Pealie/Thin-Pod-Gateway-rev-0.1/docs/observability/Thin-Pod_Memfault_nRFCloud_PR_Notes.md

# Pull Request Notes: Memfault / nRF Cloud Observability Evaluation

## PR title

Add Memfault nRF Cloud observability evaluation

## PR base and compare branches

```text
base:    gateway-rev0.1-completion-checklist
compare: memfault-nrfcloud-evaluation
```

## PR description

Adds a bounded evaluation of Memfault / nRF Cloud as an optional observability and OTA layer for the Thin-Pod Gateway / Nordic / Zephyr path.

The document positions Memfault / nRF Cloud as suitable for firmware health, reboot diagnostics, crash capture, update history and fleet-level operational metrics, while explicitly keeping the project’s open telemetry, DSP feature extraction, vibration logging and predictive-maintenance analysis pipeline independent.

## Added

- `docs/observability/Thin-Pod_Memfault_nRFCloud_Evaluation.md`

## Scope

This is a documentation-only change.

No firmware, hardware, schematic, PCB, Gateway interface, UWB transport or telemetry-schema changes are introduced by this PR.

## Notes

Memfault / nRF Cloud is treated as optional and non-core.

The open reproducibility path remains:

- local logging;
- Gateway telemetry;
- DSP feature records;
- vibration-analysis outputs;
- repository-held validation evidence;
- CSV / JSON export where appropriate.

The document makes clear that Memfault / nRF Cloud should be used to observe device and firmware health, not to define the core predictive-maintenance data path.

## Recommended conclusion

Memfault / nRF Cloud is suitable as an optional Nordic / Zephyr observability and OTA layer for Thin-Pod nodes and Gateway-side Nordic modules. It should be used for firmware health, reboot diagnostics, crash capture, update history and fleet-level operational metrics. It should not replace the project’s open telemetry, DSP feature extraction, vibration-data logging or predictive-maintenance analysis pipeline.

## Suggested review checklist

- [ ] The document is correctly located under `docs/observability/`.
- [ ] The integration is clearly described as optional.
- [ ] The core Thin-Pod telemetry and DSP path remains open and independent.
- [ ] No credentials, API keys, cloud project IDs or private Memfault / nRF Cloud values are included.
- [ ] The document does not imply that Memfault / nRF Cloud is required for OSHWA reproducibility.
- [ ] The branch contains only the intended documentation file.

## Suggested merge action

If the PR diff shows only:

```text
A       docs/observability/Thin-Pod_Memfault_nRFCloud_Evaluation.md
```

then the PR is clean and suitable to merge into:

```text
gateway-rev0.1-completion-checklist
```
