Pealie/Thin-Pod-Gateway-rev-0.1/images/GPIO_Probe_PuTTY.png

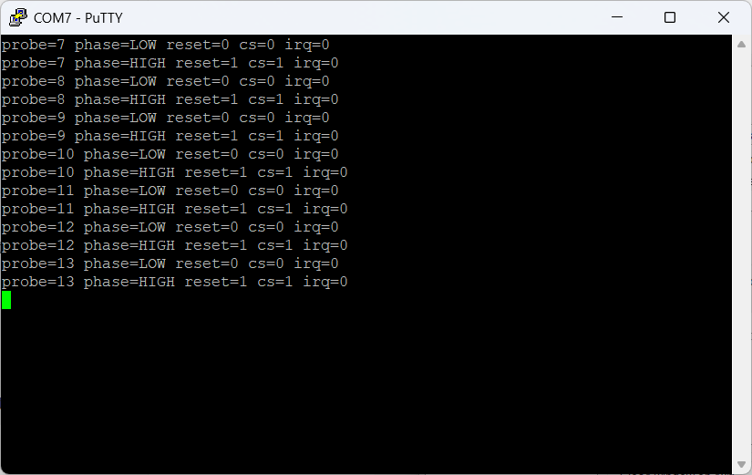
images/GPIO_Probe_PuTTY.png
