Pealie/Thin-Pod-Gateway-rev-0.1/images/Hello_World.png

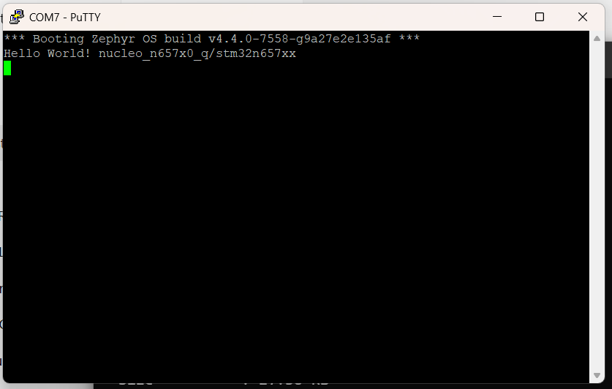
images/Hello_World.png
