Pealie/Thin-Pod-Gateway-rev-0.1/images/TP6_READY_rail_level_after_reflow_2026-07-11.jpeg

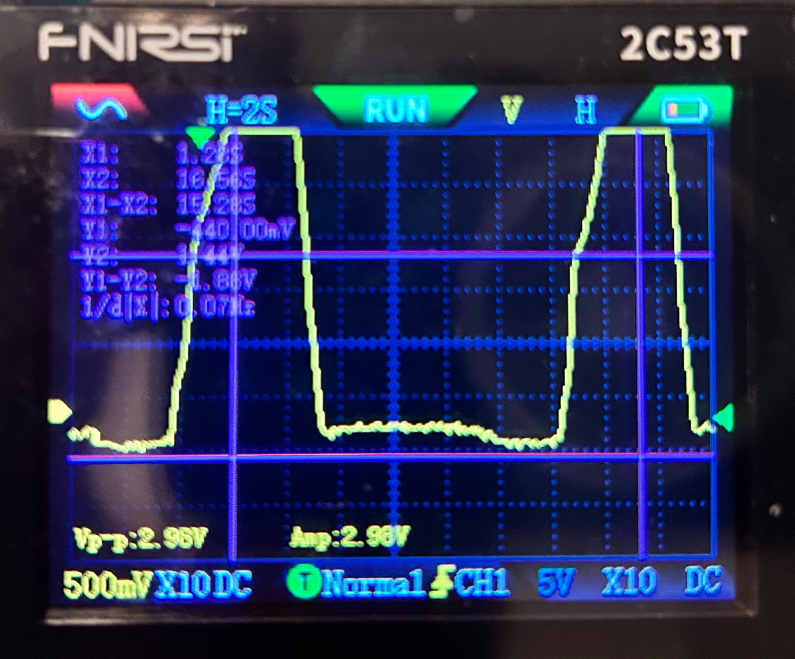
images/TP6_READY_rail_level_after_reflow_2026-07-11.jpeg
