Pealie/Thin-Pod-Gateway-rev-0.1/docs/validation/cad/rev0.1/Gerber_Drill_Inspection_Record.md

# Thin-Pod Gateway rev 0.1 Gerber and drill inspection record

**Project:** Thin-Pod Gateway  
**Release:** rev 0.1  
**Manufactured carrier identity:** rev 0.1f  
**Inspection tool:** KiCad Gerber Viewer  
**Inspection status:** PASS

## Inspection basis

The Gerber and drill package used for the manufactured Thin-Pod Gateway rev 0.1f carrier was inspected in a Gerber viewer before the fabrication order was placed. The resulting PCB was manufactured, assembled and subsequently demonstrated through powered bring-up, host-interface validation and a matched Gateway-to-Node UWB exchange.

The published revision-labelled release under `hardware/fabrication/rev0.1/` preserves the intended electrical and geometric design of that manufactured carrier.

## Inspection record

The following outputs were loaded and reviewed together:

- front and back copper;
- front and back solder mask;
- front and back solder paste;
- front and back silkscreen;
- board outline;
- plated through-hole drill data and drill map;
- non-plated through-hole drill data and drill map;
- Gerber job metadata.

The inspection confirmed:

- common origin and alignment across copper, mask, legend, outline and drill data;
- no unintended mirroring or layer displacement;
- complete board outline and intended mounting geometry;
- plated holes aligned with connector, component and test-point pads;
- non-plated holes aligned with mounting and mechanical features;
- solder-mask openings aligned with intended exposed pads;
- legible silkscreen and board identification;
- module-interface geometry consistent with the manufactured and functioning carrier;
- no obvious fabrication-output defect affecting manufacture or assembly.

## Release relationship

The regenerated release outputs use project revision `0.1` and a repository-relative output path. These metadata and portability changes introduced no intentional electrical or geometric change from the manufactured rev 0.1f carrier.

## Result

**PASS:** Gerber and drill inspection was completed before manufacture, the PCB was successfully manufactured and assembled, and subsequent hardware and RF validation demonstrated the intended carrier-board function.
